openvlc/OpenVLC/OpenVLC_VL_IR/Driver/vlc.mod.c

#include <linux/module.h>
#include <linux/vermagic.h>
#include <linux/compiler.h>

MODULE_INFO(vermagic, VERMAGIC_STRING);

__visible struct module __this_module
__attribute__((section(".gnu.linkonce.this_module"))) = {
	.name = KBUILD_MODNAME,
	.init = init_module,
#ifdef CONFIG_MODULE_UNLOAD
	.exit = cleanup_module,
#endif
	.arch = MODULE_ARCH_INIT,
};

static const struct modversion_info ____versions[]
__used
__attribute__((section("__versions"))) = {
	{ 0x2cce4d13, __VMLINUX_SYMBOL_STR(module_layout) },
	{ 0x33418265, __VMLINUX_SYMBOL_STR(kmalloc_caches) },
	{ 0x12da5bb2, __VMLINUX_SYMBOL_STR(__kmalloc) },
	{ 0xff178f6, __VMLINUX_SYMBOL_STR(__aeabi_idivmod) },
	{ 0x7494d5f5, __VMLINUX_SYMBOL_STR(param_ops_int) },
	{ 0x2e5810c6, __VMLINUX_SYMBOL_STR(__aeabi_unwind_cpp_pr1) },
	{ 0xa1d55e90, __VMLINUX_SYMBOL_STR(_raw_spin_lock_bh) },
	{ 0xb1ad28e0, __VMLINUX_SYMBOL_STR(__gnu_mcount_nc) },
	{ 0xf4fd3fc, __VMLINUX_SYMBOL_STR(mutex_unlock) },
	{ 0xc890baa4, __VMLINUX_SYMBOL_STR(kthread_create_on_node) },
	{ 0x7d11c268, __VMLINUX_SYMBOL_STR(jiffies) },
	{ 0x343a1a8, __VMLINUX_SYMBOL_STR(__list_add) },
	{ 0xf55ac006, __VMLINUX_SYMBOL_STR(__netdev_alloc_skb) },
	{ 0x87c29eab, __VMLINUX_SYMBOL_STR(netif_rx) },
	{ 0xfa2a45e, __VMLINUX_SYMBOL_STR(__memzero) },
	{ 0xf8f58676, __VMLINUX_SYMBOL_STR(netif_tx_wake_queue) },
	{ 0x27e1a049, __VMLINUX_SYMBOL_STR(printk) },
	{ 0x607b8a4e, __VMLINUX_SYMBOL_STR(kthread_stop) },
	{ 0x28f77f54, __VMLINUX_SYMBOL_STR(free_netdev) },
	{ 0xf808c4bc, __VMLINUX_SYMBOL_STR(register_netdev) },
	{ 0x9e9fdd9d, __VMLINUX_SYMBOL_STR(memunmap) },
	{ 0x20bf2e6f, __VMLINUX_SYMBOL_STR(skb_push) },
	{ 0x5136d7f4, __VMLINUX_SYMBOL_STR(mutex_lock) },
	{ 0x521445b, __VMLINUX_SYMBOL_STR(list_del) },
	{ 0x2196324, __VMLINUX_SYMBOL_STR(__aeabi_idiv) },
	{ 0x12a38747, __VMLINUX_SYMBOL_STR(usleep_range) },
	{ 0xdd3916ac, __VMLINUX_SYMBOL_STR(_raw_spin_unlock_bh) },
	{ 0xdb7305a1, __VMLINUX_SYMBOL_STR(__stack_chk_fail) },
	{ 0x6126f734, __VMLINUX_SYMBOL_STR(alloc_netdev_mqs) },
	{ 0xb0b154c2, __VMLINUX_SYMBOL_STR(wake_up_process) },
	{ 0x3a8cd40c, __VMLINUX_SYMBOL_STR(kmem_cache_alloc_trace) },
	{ 0xc65537d0, __VMLINUX_SYMBOL_STR(memremap) },
	{ 0xb3f7646e, __VMLINUX_SYMBOL_STR(kthread_should_stop) },
	{ 0x37a0cba, __VMLINUX_SYMBOL_STR(kfree) },
	{ 0x9d669763, __VMLINUX_SYMBOL_STR(memcpy) },
	{ 0x6128b5fc, __VMLINUX_SYMBOL_STR(__printk_ratelimit) },
	{ 0xf8d1965a, __VMLINUX_SYMBOL_STR(unregister_netdev) },
	{ 0x8f678b07, __VMLINUX_SYMBOL_STR(__stack_chk_guard) },
	{ 0x676bbc0f, __VMLINUX_SYMBOL_STR(_set_bit) },
	{ 0x99bb8806, __VMLINUX_SYMBOL_STR(memmove) },
	{ 0x51e1e14f, __VMLINUX_SYMBOL_STR(consume_skb) },
	{ 0x49ebacbd, __VMLINUX_SYMBOL_STR(_clear_bit) },
	{ 0xb40eb3c3, __VMLINUX_SYMBOL_STR(skb_put) },
};

static const char __module_depends[]
__used
__attribute__((section(".modinfo"))) =
"depends=";
